stsukesh/sony-mhc-gn1300d-5.1-revival/tools/build_perfect_kicad_system.py

#!/usr/bin/env python3
"""
build_perfect_kicad_system.py
Generates the complete, pristine KiCad 10 hardware files for the Sony MHC-GN1300D 5.1 Revival.
Guarantees 100% clean loading in KiCad GUI and passing kicad-cli sch/pcb tools.
"""

import os
import uuid
import subprocess

BASE = "/run/media/stsukesh/Work/Revive SonyAudio sytem/hardware/sony-5.1-revival"
os.makedirs(f"{BASE}/libs", exist_ok=True)

ROOT_UUID = "936307ec-ff2e-4b68-b34e-0a0684a0c8b0"
SHEET_UUIDS = {
    "power_supply": "00000000-0000-0000-0000-000000000001",
    "amplifier": "00000000-0000-0000-0000-000000000002",
    "crossover_input": "00000000-0000-0000-0000-000000000003",
    "controller": "00000000-0000-0000-0000-000000000004",
    "protection": "00000000-0000-0000-0000-000000000005"
}

def make_uid():
    return str(uuid.uuid4())

# -------------------------------------------------------------
# 1. WRITE COMPLETE CUSTOM SYMBOL LIBRARY (sony-revival.kicad_sym)
# -------------------------------------------------------------
def build_custom_symbol_library():
    sym_path = f"{BASE}/libs/sony-revival.kicad_sym"
    content = """(kicad_symbol_lib
	(version 20231120)
	(generator "eeschema")
	(generator_version "10.0")
	(symbol "TPA3116D2"
		(in_bom yes)
		(on_board yes)
		(property "Reference" "U" (at -15.24 35.56 0) (effects (font (size 1.27 1.27))))
		(property "Value" "TPA3116D2" (at 5.08 35.56 0) (effects (font (size 1.27 1.27))))
		(property "Footprint" "Package_SO:HTSSOP-32-1EP_6.1x11mm_P0.65mm_EP5.2x11mm" (at 0 -40.64 0) (effects (font (size 1.27 1.27)) hide))
		(property "Datasheet" "http://www.ti.com/lit/ds/symlink/tpa3116d2.pdf" (at 0 -43.18 0) (effects (font (size 1.27 1.27)) hide))
		(property "Description" "50W Stereo / 100W Mono Class-D Audio Amplifier, HTSSOP-32" (at 0 -45.72 0) (effects (font (size 1.27 1.27)) hide))
		(symbol "TPA3116D2_0_1"
			(rectangle (start -15.24 33.02) (end 15.24 -38.1) (stroke (width 0.254) (type default)) (fill (type background)))
		)
		(symbol "TPA3116D2_1_1"
			(pin input line (at -17.78 30.48 0) (length 2.54) (name "MODSEL" (effects (font (size 1.27 1.27)))) (number "1" (effects (font (size 1.27 1.27)))))
			(pin input line (at -17.78 27.94 0) (length 2.54) (name "~{SD}" (effects (font (size 1.27 1.27)))) (number "2" (effects (font (size 1.27 1.27)))))
			(pin open_collector line (at -17.78 25.4 0) (length 2.54) (name "~{FAULT}" (effects (font (size 1.27 1.27)))) (number "3" (effects (font (size 1.27 1.27)))))
			(pin input line (at -17.78 20.32 0) (length 2.54) (name "INPL" (effects (font (size 1.27 1.27)))) (number "4" (effects (font (size 1.27 1.27)))))
			(pin input line (at -17.78 17.78 0) (length 2.54) (name "INNL" (effects (font (size 1.27 1.27)))) (number "5" (effects (font (size 1.27 1.27)))))
			(pin input line (at -17.78 12.7 0) (length 2.54) (name "PLIMIT" (effects (font (size 1.27 1.27)))) (number "6" (effects (font (size 1.27 1.27)))))
			(pin power_out line (at -17.78 7.62 0) (length 2.54) (name "GVDD" (effects (font (size 1.27 1.27)))) (number "7" (effects (font (size 1.27 1.27)))))
			(pin input line (at -17.78 2.54 0) (length 2.54) (name "GAIN/SLV" (effects (font (size 1.27 1.27)))) (number "8" (effects (font (size 1.27 1.27)))))
			(pin power_in line (at 0 -40.64 90) (length 2.54) (name "AGND" (effects (font (size 1.27 1.27)))) (number "9" (effects (font (size 1.27 1.27)))))
			(pin input line (at -17.78 -2.54 0) (length 2.54) (name "INNR" (effects (font (size 1.27 1.27)))) (number "10" (effects (font (size 1.27 1.27)))))
			(pin input line (at -17.78 -5.08 0) (length 2.54) (name "INPR" (effects (font (size 1.27 1.27)))) (number "11" (effects (font (size 1.27 1.27)))))
			(pin power_in line (at 17.78 30.48 180) (length 2.54) (name "PVCC" (effects (font (size 1.27 1.27)))) (number "16" (effects (font (size 1.27 1.27)))))
			(pin power_in line (at 17.78 27.94 180) (length 2.54) (name "PVCC" (effects (font (size 1.27 1.27)))) (number "17" (effects (font (size 1.27 1.27)))))
			(pin passive line (at 17.78 22.86 180) (length 2.54) (name "BSPR" (effects (font (size 1.27 1.27)))) (number "18" (effects (font (size 1.27 1.27)))))
			(pin output line (at 17.78 20.32 180) (length 2.54) (name "OUTPR" (effects (font (size 1.27 1.27)))) (number "19" (effects (font (size 1.27 1.27)))))
			(pin power_in line (at 2.54 -40.64 90) (length 2.54) (name "PGND" (effects (font (size 1.27 1.27)))) (number "20" (effects (font (size 1.27 1.27)))))
			(pin output line (at 17.78 15.24 180) (length 2.54) (name "OUTNR" (effects (font (size 1.27 1.27)))) (number "21" (effects (font (size 1.27 1.27)))))
			(pin passive line (at 17.78 12.7 180) (length 2.54) (name "BSNR" (effects (font (size 1.27 1.27)))) (number "22" (effects (font (size 1.27 1.27)))))
			(pin passive line (at 17.78 0 180) (length 2.54) (name "BSNL" (effects (font (size 1.27 1.27)))) (number "25" (effects (font (size 1.27 1.27)))))
			(pin output line (at 17.78 -2.54 180) (length 2.54) (name "OUTNL" (effects (font (size 1.27 1.27)))) (number "26" (effects (font (size 1.27 1.27)))))
			(pin power_in line (at 5.08 -40.64 90) (length 2.54) (name "PGND" (effects (font (size 1.27 1.27)))) (number "27" (effects (font (size 1.27 1.27)))))
			(pin output line (at 17.78 -7.62 180) (length 2.54) (name "OUTPL" (effects (font (size 1.27 1.27)))) (number "28" (effects (font (size 1.27 1.27)))))
			(pin passive line (at 17.78 -10.16 180) (length 2.54) (name "BSPL" (effects (font (size 1.27 1.27)))) (number "29" (effects (font (size 1.27 1.27)))))
			(pin power_in line (at 17.78 -15.24 180) (length 2.54) (name "PVCC" (effects (font (size 1.27 1.27)))) (number "30" (effects (font (size 1.27 1.27)))))
			(pin power_in line (at 17.78 -17.78 180) (length 2.54) (name "PVCC" (effects (font (size 1.27 1.27)))) (number "31" (effects (font (size 1.27 1.27)))))
			(pin power_in line (at -2.54 -40.64 90) (length 2.54) (name "AVCC" (effects (font (size 1.27 1.27)))) (number "32" (effects (font (size 1.27 1.27)))))
		)
	)
	(symbol "MCP4252"
		(in_bom yes)
		(on_board yes)
		(property "Reference" "U" (at -10.16 20.32 0) (effects (font (size 1.27 1.27))))
		(property "Value" "MCP4252" (at 5.08 20.32 0) (effects (font (size 1.27 1.27))))
		(property "Footprint" "Package_SO:SOIC-14_3.9x8.7mm_P1.27mm" (at 0 -22.86 0) (effects (font (size 1.27 1.27)) hide))
		(property "Datasheet" "https://ww1.microchip.com/downloads/en/DeviceDoc/22060b.pdf" (at 0 -25.4 0) (effects (font (size 1.27 1.27)) hide))
		(property "Description" "7/8-Bit Dual SPI Digital POT with Non-Volatile Memory" (at 0 -27.94 0) (effects (font (size 1.27 1.27)) hide))
		(symbol "MCP4252_0_1"
			(rectangle (start -10.16 17.78) (end 10.16 -20.32) (stroke (width 0.254) (type default)) (fill (type background)))
		)
		(symbol "MCP4252_1_1"
			(pin input line (at -12.7 15.24 0) (length 2.54) (name "~{CS}" (effects (font (size 1.27 1.27)))) (number "1" (effects (font (size 1.27 1.27)))))
			(pin input line (at -12.7 12.7 0) (length 2.54) (name "SCK" (effects (font (size 1.27 1.27)))) (number "2" (effects (font (size 1.27 1.27)))))
			(pin input line (at -12.7 10.16 0) (length 2.54) (name "SDI" (effects (font (size 1.27 1.27)))) (number "3" (effects (font (size 1.27 1.27)))))
			(pin power_in line (at 0 -22.86 90) (length 2.54) (name "VSS" (effects (font (size 1.27 1.27)))) (number "4" (effects (font (size 1.27 1.27)))))
			(pin passive line (at 12.7 5.08 180) (length 2.54) (name "P1B" (effects (font (size 1.27 1.27)))) (number "5" (effects (font (size 1.27 1.27)))))
			(pin passive line (at 12.7 7.62 180) (length 2.54) (name "P1W" (effects (font (size 1.27 1.27)))) (number "6" (effects (font (size 1.27 1.27)))))
			(pin passive line (at 12.7 10.16 180) (length 2.54) (name "P1A" (effects (font (size 1.27 1.27)))) (number "7" (effects (font (size 1.27 1.27)))))
			(pin passive line (at 12.7 -5.08 180) (length 2.54) (name "P0A" (effects (font (size 1.27 1.27)))) (number "8" (effects (font (size 1.27 1.27)))))
			(pin passive line (at 12.7 -7.62 180) (length 2.54) (name "P0W" (effects (font (size 1.27 1.27)))) (number "9" (effects (font (size 1.27 1.27)))))
			(pin passive line (at 12.7 -10.16 180) (length 2.54) (name "P0B" (effects (font (size 1.27 1.27)))) (number "10" (effects (font (size 1.27 1.27)))))
			(pin input line (at -12.7 0 0) (length 2.54) (name "~{WP}" (effects (font (size 1.27 1.27)))) (number "11" (effects (font (size 1.27 1.27)))))
			(pin input line (at -12.7 -2.54 0) (length 2.54) (name "~{SHDN}" (effects (font (size 1.27 1.27)))) (number "12" (effects (font (size 1.27 1.27)))))
			(pin output line (at -12.7 -7.62 0) (length 2.54) (name "SDO" (effects (font (size 1.27 1.27)))) (number "13" (effects (font (size 1.27 1.27)))))
			(pin power_in line (at 0 20.32 270) (length 2.54) (name "VDD" (effects (font (size 1.27 1.27)))) (number "14" (effects (font (size 1.27 1.27)))))
		)
	)
	(symbol "CD4052"
		(in_bom yes)
		(on_board yes)
		(property "Reference" "U" (at -10.16 22.86 0) (effects (font (size 1.27 1.27))))
		(property "Value" "CD4052" (at 5.08 22.86 0) (effects (font (size 1.27 1.27))))
		(property "Footprint" "Package_SO:SOIC-16_3.9x9.9mm_P1.27mm" (at 0 -25.4 0) (effects (font (size 1.27 1.27)) hide))
		(property "Datasheet" "http://www.ti.com/lit/ds/symlink/cd4052b.pdf" (at 0 -27.94 0) (effects (font (size 1.27 1.27)) hide))
		(property "Description" "Dual 4-Channel Analog Multiplexer / Demultiplexer" (at 0 -30.48 0) (effects (font (size 1.27 1.27)) hide))
		(symbol "CD4052_0_1"
			(rectangle (start -10.16 20.32) (end 10.16 -22.86) (stroke (width 0.254) (type default)) (fill (type background)))
		)
		(symbol "CD4052_1_1"
			(pin bidirectional line (at 12.7 15.24 180) (length 2.54) (name "Y0" (effects (font (size 1.27 1.27)))) (number "1" (effects (font (size 1.27 1.27)))))
			(pin bidirectional line (at 12.7 10.16 180) (length 2.54) (name "Y2" (effects (font (size 1.27 1.27)))) (number "2" (effects (font (size 1.27 1.27)))))
			(pin bidirectional line (at -12.7 12.7 0) (length 2.54) (name "Y_COM" (effects (font (size 1.27 1.27)))) (number "3" (effects (font (size 1.27 1.27)))))
			(pin bidirectional line (at 12.7 7.62 180) (length 2.54) (name "Y3" (effects (font (size 1.27 1.27)))) (number "4" (effects (font (size 1.27 1.27)))))
			(pin bidirectional line (at 12.7 12.7 180) (length 2.54) (name "Y1" (effects (font (size 1.27 1.27)))) (number "5" (effects (font (size 1.27 1.27)))))
			(pin input line (at -12.7 -15.24 0) (length 2.54) (name "INH" (effects (font (size 1.27 1.27)))) (number "6" (effects (font (size 1.27 1.27)))))
			(pin power_in line (at 2.54 -25.4 90) (length 2.54) (name "VEE" (effects (font (size 1.27 1.27)))) (number "7" (effects (font (size 1.27 1.27)))))
			(pin power_in line (at -2.54 -25.4 90) (length 2.54) (name "VSS" (effects (font (size 1.27 1.27)))) (number "8" (effects (font (size 1.27 1.27)))))
			(pin input line (at -12.7 -12.7 0) (length 2.54) (name "B" (effects (font (size 1.27 1.27)))) (number "9" (effects (font (size 1.27 1.27)))))
			(pin input line (at -12.7 -10.16 0) (length 2.54) (name "A" (effects (font (size 1.27 1.27)))) (number "10" (effects (font (size 1.27 1.27)))))
			(pin bidirectional line (at 12.7 -7.62 180) (length 2.54) (name "X3" (effects (font (size 1.27 1.27)))) (number "11" (effects (font (size 1.27 1.27)))))
			(pin bidirectional line (at 12.7 0 180) (length 2.54) (name "X0" (effects (font (size 1.27 1.27)))) (number "12" (effects (font (size 1.27 1.27)))))
			(pin bidirectional line (at -12.7 -2.54 0) (length 2.54) (name "X_COM" (effects (font (size 1.27 1.27)))) (number "13" (effects (font (size 1.27 1.27)))))
			(pin bidirectional line (at 12.7 -2.54 180) (length 2.54) (name "X1" (effects (font (size 1.27 1.27)))) (number "14" (effects (font (size 1.27 1.27)))))
			(pin bidirectional line (at 12.7 -5.08 180) (length 2.54) (name "X2" (effects (font (size 1.27 1.27)))) (number "15" (effects (font (size 1.27 1.27)))))
			(pin power_in line (at 0 22.86 270) (length 2.54) (name "VDD" (effects (font (size 1.27 1.27)))) (number "16" (effects (font (size 1.27 1.27)))))
		)
	)
	(symbol "QCC3008_MODULE"
		(in_bom yes)
		(on_board yes)
		(property "Reference" "U" (at -10.16 17.78 0) (effects (font (size 1.27 1.27))))
		(property "Value" "QCC3008_MODULE" (at 5.08 17.78 0) (effects (font (size 1.27 1.27))))
		(property "Footprint" "Connector_PinHeader_2.54mm:PinHeader_1x12_P2.54mm_Vertical" (at 0 -20.32 0) (effects (font (size 1.27 1.27)) hide))
		(property "Datasheet" "" (at 0 -22.86 0) (effects (font (size 1.27 1.27)) hide))
		(property "Description" "Qualcomm QCC3008 Bluetooth 5.0 Audio Module (aptX / aptX-LL)" (at 0 -25.4 0) (effects (font (size 1.27 1.27)) hide))
		(symbol "QCC3008_MODULE_0_1"
			(rectangle (start -10.16 15.24) (end 10.16 -17.78) (stroke (width 0.254) (type default)) (fill (type background)))
		)
		(symbol "QCC3008_MODULE_1_1"
			(pin power_in line (at 0 17.78 270) (length 2.54) (name "3V3" (effects (font (size 1.27 1.27)))) (number "1" (effects (font (size 1.27 1.27)))))
			(pin power_in line (at 0 -20.32 90) (length 2.54) (name "GND" (effects (font (size 1.27 1.27)))) (number "2" (effects (font (size 1.27 1.27)))))
			(pin output line (at 12.7 12.7 180) (length 2.54) (name "AOUTL_P" (effects (font (size 1.27 1.27)))) (number "3" (effects (font (size 1.27 1.27)))))
			(pin output line (at 12.7 10.16 180) (length 2.54) (name "AOUTL_N" (effects (font (size 1.27 1.27)))) (number "4" (effects (font (size 1.27 1.27)))))
			(pin output line (at 12.7 5.08 180) (length 2.54) (name "AOUTR_P" (effects (font (size 1.27 1.27)))) (number "5" (effects (font (size 1.27 1.27)))))
			(pin output line (at 12.7 2.54 180) (length 2.54) (name "AOUTR_N" (effects (font (size 1.27 1.27)))) (number "6" (effects (font (size 1.27 1.27)))))
			(pin output line (at 12.7 -2.54 180) (length 2.54) (name "SPDIF" (effects (font (size 1.27 1.27)))) (number "7" (effects (font (size 1.27 1.27)))))
			(pin input line (at -12.7 10.16 0) (length 2.54) (name "KEY" (effects (font (size 1.27 1.27)))) (number "8" (effects (font (size 1.27 1.27)))))
			(pin output line (at -12.7 5.08 0) (length 2.54) (name "LED1" (effects (font (size 1.27 1.27)))) (number "9" (effects (font (size 1.27 1.27)))))
			(pin output line (at -12.7 2.54 0) (length 2.54) (name "LED2" (effects (font (size 1.27 1.27)))) (number "10" (effects (font (size 1.27 1.27)))))
			(pin output line (at -12.7 -7.62 0) (length 2.54) (name "TX" (effects (font (size 1.27 1.27)))) (number "11" (effects (font (size 1.27 1.27)))))
			(pin input line (at -12.7 -10.16 0) (length 2.54) (name "RX" (effects (font (size 1.27 1.27)))) (number "12" (effects (font (size 1.27 1.27)))))
		)
	)
	(symbol "RELAY_SPST"
		(in_bom yes)
		(on_board yes)
		(property "Reference" "K" (at -7.62 10.16 0) (effects (font (size 1.27 1.27))))
		(property "Value" "RELAY_SPST" (at 2.54 10.16 0) (effects (font (size 1.27 1.27))))
		(property "Footprint" "Relay_THT:Relay_SPST_SANYOU_SRD_Series_Form_A" (at 0 -12.7 0) (effects (font (size 1.27 1.27)) hide))
		(property "Datasheet" "" (at 0 -15.24 0) (effects (font (size 1.27 1.27)) hide))
		(property "Description" "SPST Power Relay 10A 250VAC, 5V Coil" (at 0 -17.78 0) (effects (font (size 1.27 1.27)) hide))
		(symbol "RELAY_SPST_0_1"
			(rectangle (start -7.62 7.62) (end 7.62 -10.16) (stroke (width 0.254) (type default)) (fill (type background)))
		)
		(symbol "RELAY_SPST_1_1"
			(pin passive line (at -10.16 5.08 0) (length 2.54) (name "COIL+" (effects (font (size 1.27 1.27)))) (number "1" (effects (font (size 1.27 1.27)))))
			(pin passive line (at -10.16 -5.08 0) (length 2.54) (name "COIL-" (effects (font (size 1.27 1.27)))) (number "2" (effects (font (size 1.27 1.27)))))
			(pin passive line (at 10.16 5.08 180) (length 2.54) (name "COM" (effects (font (size 1.27 1.27)))) (number "3" (effects (font (size 1.27 1.27)))))
			(pin passive line (at 10.16 -5.08 180) (length 2.54) (name "NO" (effects (font (size 1.27 1.27)))) (number "4" (effects (font (size 1.27 1.27)))))
		)
	)
	(symbol "TLE2426"
		(in_bom yes)
		(on_board yes)
		(property "Reference" "U" (at -7.62 10.16 0) (effects (font (size 1.27 1.27))))
		(property "Value" "TLE2426" (at 2.54 10.16 0) (effects (font (size 1.27 1.27))))
		(property "Footprint" "Package_TO_SOT_THT:TO-92_Inline" (at 0 -12.7 0) (effects (font (size 1.27 1.27)) hide))
		(property "Datasheet" "http://www.ti.com/lit/ds/symlink/tle2426.pdf" (at 0 -15.24 0) (effects (font (size 1.27 1.27)) hide))
		(property "Description" "The 'Rail Splitter' Precision Virtual Ground" (at 0 -17.78 0) (effects (font (size 1.27 1.27)) hide))
		(symbol "TLE2426_0_1"
			(rectangle (start -7.62 7.62) (end 7.62 -10.16) (stroke (width 0.254) (type default)) (fill (type background)))
		)
		(symbol "TLE2426_1_1"
			(pin power_in line (at 0 10.16 270) (length 2.54) (name "IN" (effects (font (size 1.27 1.27)))) (number "1" (effects (font (size 1.27 1.27)))))
			(pin power_out line (at 10.16 0 180) (length 2.54) (name "OUT" (effects (font (size 1.27 1.27)))) (number "2" (effects (font (size 1.27 1.27)))))
			(pin power_in line (at 0 -12.7 90) (length 2.54) (name "COM" (effects (font (size 1.27 1.27)))) (number "3" (effects (font (size 1.27 1.27)))))
		)
	)
	(symbol "LM2596_5V"
		(in_bom yes)
		(on_board yes)
		(property "Reference" "U" (at -10.16 12.7 0) (effects (font (size 1.27 1.27))))
		(property "Value" "LM2596_5V" (at 2.54 12.7 0) (effects (font (size 1.27 1.27))))
		(property "Footprint" "Package_TO_SOT_SMD:TO-263-5_TabPin3" (at 0 -15.24 0) (effects (font (size 1.27 1.27)) hide))
		(property "Datasheet" "http://www.ti.com/lit/ds/symlink/lm2596.pdf" (at 0 -17.78 0) (effects (font (size 1.27 1.27)) hide))
		(property "Description" "SIMPLE SWITCHER 3A Step-Down Voltage Regulator, 5.0V Output" (at 0 -20.32 0) (effects (font (size 1.27 1.27)) hide))
		(symbol "LM2596_5V_0_1"
			(rectangle (start -10.16 10.16) (end 10.16 -12.7) (stroke (width 0.254) (type default)) (fill (type background)))
		)
		(symbol "LM2596_5V_1_1"
			(pin power_in line (at -12.7 7.62 0) (length 2.54) (name "VIN" (effects (font (size 1.27 1.27)))) (number "1" (effects (font (size 1.27 1.27)))))
			(pin power_out line (at 12.7 7.62 180) (length 2.54) (name "OUT" (effects (font (size 1.27 1.27)))) (number "2" (effects (font (size 1.27 1.27)))))
			(pin power_in line (at 0 -15.24 90) (length 2.54) (name "GND" (effects (font (size 1.27 1.27)))) (number "3" (effects (font (size 1.27 1.27)))))
			(pin input line (at 12.7 -5.08 180) (length 2.54) (name "FB" (effects (font (size 1.27 1.27)))) (number "4" (effects (font (size 1.27 1.27)))))
			(pin input line (at -12.7 -5.08 0) (length 2.54) (name "~{ON}/OFF" (effects (font (size 1.27 1.27)))) (number "5" (effects (font (size 1.27 1.27)))))
		)
	)
	(symbol "ESP32_WROOM_32"
		(in_bom yes)
		(on_board yes)
		(property "Reference" "U" (at -15.24 30.48 0) (effects (font (size 1.27 1.27))))
		(property "Value" "ESP32_WROOM_32" (at 5.08 30.48 0) (effects (font (size 1.27 1.27))))
		(property "Footprint" "RF_Module:ESP32-WROOM-32" (at 0 -33.02 0) (effects (font (size 1.27 1.27)) hide))
		(property "Datasheet" "https://www.espressif.com/sites/default/files/documentation/esp32-wroom-32_datasheet_en.pdf" (at 0 -35.56 0) (effects (font (size 1.27 1.27)) hide))
		(property "Description" "RF Module, ESP32-D0WDQ6 SoC, Wi-Fi 802.11b/g/n, Bluetooth, BLE, 32-bit, 2.7-3.6V" (at 0 -38.1 0) (effects (font (size 1.27 1.27)) hide))
		(symbol "ESP32_WROOM_32_0_1"
			(rectangle (start -15.24 27.94) (end 15.24 -30.48) (stroke (width 0.254) (type default)) (fill (type background)))
		)
		(symbol "ESP32_WROOM_32_1_1"
			(pin power_in line (at -17.78 25.4 0) (length 2.54) (name "3V3" (effects (font (size 1.27 1.27)))) (number "1" (effects (font (size 1.27 1.27)))))
			(pin input line (at -17.78 22.86 0) (length 2.54) (name "EN" (effects (font (size 1.27 1.27)))) (number "2" (effects (font (size 1.27 1.27)))))
			(pin input line (at -17.78 20.32 0) (length 2.54) (name "SENSOR_VP" (effects (font (size 1.27 1.27)))) (number "3" (effects (font (size 1.27 1.27)))))
			(pin input line (at -17.78 17.78 0) (length 2.54) (name "SENSOR_VN" (effects (font (size 1.27 1.27)))) (number "4" (effects (font (size 1.27 1.27)))))
			(pin input line (at -17.78 15.24 0) (length 2.54) (name "IO34" (effects (font (size 1.27 1.27)))) (number "5" (effects (font (size 1.27 1.27)))))
			(pin input line (at -17.78 12.7 0) (length 2.54) (name "IO35" (effects (font (size 1.27 1.27)))) (number "6" (effects (font (size 1.27 1.27)))))
			(pin bidirectional line (at -17.78 10.16 0) (length 2.54) (name "IO32" (effects (font (size 1.27 1.27)))) (number "7" (effects (font (size 1.27 1.27)))))
			(pin bidirectional line (at -17.78 7.62 0) (length 2.54) (name "IO33" (effects (font (size 1.27 1.27)))) (number "8" (effects (font (size 1.27 1.27)))))
			(pin bidirectional line (at -17.78 5.08 0) (length 2.54) (name "IO25" (effects (font (size 1.27 1.27)))) (number "9" (effects (font (size 1.27 1.27)))))
			(pin bidirectional line (at -17.78 2.54 0) (length 2.54) (name "IO26" (effects (font (size 1.27 1.27)))) (number "10" (effects (font (size 1.27 1.27)))))
			(pin bidirectional line (at -17.78 0 0) (length 2.54) (name "IO27" (effects (font (size 1.27 1.27)))) (number "11" (effects (font (size 1.27 1.27)))))
			(pin bidirectional line (at -17.78 -2.54 0) (length 2.54) (name "IO14" (effects (font (size 1.27 1.27)))) (number "12" (effects (font (size 1.27 1.27)))))
			(pin bidirectional line (at -17.78 -5.08 0) (length 2.54) (name "IO12" (effects (font (size 1.27 1.27)))) (number "13" (effects (font (size 1.27 1.27)))))
			(pin power_in line (at -17.78 -10.16 0) (length 2.54) (name "GND" (effects (font (size 1.27 1.27)))) (number "14" (effects (font (size 1.27 1.27)))))
			(pin bidirectional line (at 17.78 -5.08 180) (length 2.54) (name "IO13" (effects (font (size 1.27 1.27)))) (number "15" (effects (font (size 1.27 1.27)))))
			(pin bidirectional line (at 17.78 -2.54 180) (length 2.54) (name "IO15" (effects (font (size 1.27 1.27)))) (number "16" (effects (font (size 1.27 1.27)))))
			(pin bidirectional line (at 17.78 0 180) (length 2.54) (name "IO2" (effects (font (size 1.27 1.27)))) (number "17" (effects (font (size 1.27 1.27)))))
			(pin bidirectional line (at 17.78 2.54 180) (length 2.54) (name "IO0" (effects (font (size 1.27 1.27)))) (number "18" (effects (font (size 1.27 1.27)))))
			(pin bidirectional line (at 17.78 5.08 180) (length 2.54) (name "IO4" (effects (font (size 1.27 1.27)))) (number "19" (effects (font (size 1.27 1.27)))))
			(pin bidirectional line (at 17.78 7.62 180) (length 2.54) (name "IO16" (effects (font (size 1.27 1.27)))) (number "20" (effects (font (size 1.27 1.27)))))
			(pin bidirectional line (at 17.78 10.16 180) (length 2.54) (name "IO17" (effects (font (size 1.27 1.27)))) (number "21" (effects (font (size 1.27 1.27)))))
			(pin bidirectional line (at 17.78 12.7 180) (length 2.54) (name "IO5" (effects (font (size 1.27 1.27)))) (number "22" (effects (font (size 1.27 1.27)))))
			(pin bidirectional line (at 17.78 15.24 180) (length 2.54) (name "IO18" (effects (font (size 1.27 1.27)))) (number "23" (effects (font (size 1.27 1.27)))))
			(pin bidirectional line (at 17.78 17.78 180) (length 2.54) (name "IO19" (effects (font (size 1.27 1.27)))) (number "24" (effects (font (size 1.27 1.27)))))
			(pin bidirectional line (at 17.78 20.32 180) (length 2.54) (name "IO21" (effects (font (size 1.27 1.27)))) (number "25" (effects (font (size 1.27 1.27)))))
			(pin bidirectional line (at 17.78 22.86 180) (length 2.54) (name "IO22" (effects (font (size 1.27 1.27)))) (number "26" (effects (font (size 1.27 1.27)))))
			(pin bidirectional line (at 17.78 25.4 180) (length 2.54) (name "IO23" (effects (font (size 1.27 1.27)))) (number "27" (effects (font (size 1.27 1.27)))))
			(pin output line (at 17.78 27.94 180) (length 2.54) (name "TXD0" (effects (font (size 1.27 1.27)))) (number "28" (effects (font (size 1.27 1.27)))))
			(pin input line (at 17.78 30.48 180) (length 2.54) (name "RXD0" (effects (font (size 1.27 1.27)))) (number "29" (effects (font (size 1.27 1.27)))))
			(pin power_in line (at 0 -33.02 90) (length 2.54) (name "GND" (effects (font (size 1.27 1.27)))) (number "38" (effects (font (size 1.27 1.27)))))
		)
	)
	(symbol "NE5532"
		(in_bom yes)
		(on_board yes)
		(property "Reference" "U" (at -7.62 12.7 0) (effects (font (size 1.27 1.27))))
		(property "Value" "NE5532" (at 2.54 12.7 0) (effects (font (size 1.27 1.27))))
		(property "Footprint" "Package_SO:SOIC-8_3.9x4.9mm_P1.27mm" (at 0 -15.24 0) (effects (font (size 1.27 1.27)) hide))
		(property "Datasheet" "http://www.ti.com/lit/ds/symlink/ne5532.pdf" (at 0 -17.78 0) (effects (font (size 1.27 1.27)) hide))
		(property "Description" "Dual Low-Noise Operational Amplifier, DIP-8/SOIC-8" (at 0 -20.32 0) (effects (font (size 1.27 1.27)) hide))
		(symbol "NE5532_0_1"
			(rectangle (start -10.16 10.16) (end 10.16 -12.7) (stroke (width 0.254) (type default)) (fill (type background)))
		)
		(symbol "NE5532_1_1"
			(pin output line (at 12.7 7.62 180) (length 2.54) (name "OUTA" (effects (font (size 1.27 1.27)))) (number "1" (effects (font (size 1.27 1.27)))))
			(pin input line (at -12.7 7.62 0) (length 2.54) (name "-INA" (effects (font (size 1.27 1.27)))) (number "2" (effects (font (size 1.27 1.27)))))
			(pin input line (at -12.7 2.54 0) (length 2.54) (name "+INA" (effects (font (size 1.27 1.27)))) (number "3" (effects (font (size 1.27 1.27)))))
			(pin power_in line (at 0 -15.24 90) (length 2.54) (name "V-" (effects (font (size 1.27 1.27)))) (number "4" (effects (font (size 1.27 1.27)))))
			(pin input line (at -12.7 -2.54 0) (length 2.54) (name "+INB" (effects (font (size 1.27 1.27)))) (number "5" (effects (font (size 1.27 1.27)))))
			(pin input line (at -12.7 -7.62 0) (length 2.54) (name "-INB" (effects (font (size 1.27 1.27)))) (number "6" (effects (font (size 1.27 1.27)))))
			(pin output line (at 12.7 -7.62 180) (length 2.54) (name "OUTB" (effects (font (size 1.27 1.27)))) (number "7" (effects (font (size 1.27 1.27)))))
			(pin power_in line (at 0 12.7 270) (length 2.54) (name "V+" (effects (font (size 1.27 1.27)))) (number "8" (effects (font (size 1.27 1.27)))))
		)
	)
	(symbol "KBU810"
		(in_bom yes)
		(on_board yes)
		(property "Reference" "BR" (at -7.62 10.16 0) (effects (font (size 1.27 1.27))))
		(property "Value" "KBU810" (at 2.54 10.16 0) (effects (font (size 1.27 1.27))))
		(property "Footprint" "Diode_THT:Diode_Bridge_Vishay_KBU" (at 0 -12.7 0) (effects (font (size 1.27 1.27)) hide))
		(property "Datasheet" "https://www.vishay.com/docs/88657/kbu8a.pdf" (at 0 -15.24 0) (effects (font (size 1.27 1.27)) hide))
		(property "Description" "Single-Phase Bridge Rectifier, 8.0A, 1000V" (at 0 -17.78 0) (effects (font (size 1.27 1.27)) hide))
		(symbol "KBU810_0_1"
			(rectangle (start -7.62 7.62) (end 7.62 -10.16) (stroke (width 0.254) (type default)) (fill (type background)))
		)
		(symbol "KBU810_1_1"
			(pin power_out line (at 10.16 5.08 180) (length 2.54) (name "+" (effects (font (size 1.27 1.27)))) (number "1" (effects (font (size 1.27 1.27)))))
			(pin passive line (at -10.16 5.08 0) (length 2.54) (name "~" (effects (font (size 1.27 1.27)))) (number "2" (effects (font (size 1.27 1.27)))))
			(pin passive line (at -10.16 -5.08 0) (length 2.54) (name "~" (effects (font (size 1.27 1.27)))) (number "3" (effects (font (size 1.27 1.27)))))
			(pin power_out line (at 10.16 -5.08 180) (length 2.54) (name "-" (effects (font (size 1.27 1.27)))) (number "4" (effects (font (size 1.27 1.27)))))
		)
	)
	(symbol "AMS1117_3V3"
		(in_bom yes)
		(on_board yes)
		(property "Reference" "U" (at -7.62 10.16 0) (effects (font (size 1.27 1.27))))
		(property "Value" "AMS1117_3V3" (at 2.54 10.16 0) (effects (font (size 1.27 1.27))))
		(property "Footprint" "Package_TO_SOT_SMD:SOT-223-3_TabPin2" (at 0 -12.7 0) (effects (font (size 1.27 1.27)) hide))
		(property "Datasheet" "http://www.advanced-monolithic.com/pdf/ds1117.pdf" (at 0 -15.24 0) (effects (font (size 1.27 1.27)) hide))
		(property "Description" "1A Low Dropout Linear Regulator, 3.3V Output" (at 0 -17.78 0) (effects (font (size 1.27 1.27)) hide))
		(symbol "AMS1117_3V3_0_1"
			(rectangle (start -7.62 7.62) (end 7.62 -10.16) (stroke (width 0.254) (type default)) (fill (type background)))
		)
		(symbol "AMS1117_3V3_1_1"
			(pin power_in line (at 0 -12.7 90) (length 2.54) (name "GND" (effects (font (size 1.27 1.27)))) (number "1" (effects (font (size 1.27 1.27)))))
			(pin power_out line (at 10.16 0 180) (length 2.54) (name "VOUT" (effects (font (size 1.27 1.27)))) (number "2" (effects (font (size 1.27 1.27)))))
			(pin power_in line (at -10.16 0 0) (length 2.54) (name "VIN" (effects (font (size 1.27 1.27)))) (number "3" (effects (font (size 1.27 1.27)))))
		)
	)
	(symbol "2N2222"
		(in_bom yes)
		(on_board yes)
		(property "Reference" "Q" (at -5.08 7.62 0) (effects (font (size 1.27 1.27))))
		(property "Value" "2N2222" (at 2.54 7.62 0) (effects (font (size 1.27 1.27))))
		(property "Footprint" "Package_TO_SOT_THT:TO-92_Inline" (at 0 -10.16 0) (effects (font (size 1.27 1.27)) hide))
		(property "Datasheet" "" (at 0 -12.7 0) (effects (font (size 1.27 1.27)) hide))
		(property "Description" "NPN BJT Transistor 40V 0.8A" (at 0 -15.24 0) (effects (font (size 1.27 1.27)) hide))
		(symbol "2N2222_0_1"
			(rectangle (start -5.08 5.08) (end 5.08 -7.62) (stroke (width 0.254) (type default)) (fill (type background)))
		)
		(symbol "2N2222_1_1"
			(pin input line (at -7.62 0 0) (length 2.54) (name "B" (effects (font (size 1.27 1.27)))) (number "1" (effects (font (size 1.27 1.27)))))
			(pin passive line (at 7.62 2.54 180) (length 2.54) (name "C" (effects (font (size 1.27 1.27)))) (number "2" (effects (font (size 1.27 1.27)))))
			(pin passive line (at 7.62 -2.54 180) (length 2.54) (name "E" (effects (font (size 1.27 1.27)))) (number "3" (effects (font (size 1.27 1.27)))))
		)
	)
	(symbol "TSOP1738"
		(in_bom yes)
		(on_board yes)
		(property "Reference" "U" (at -5.08 7.62 0) (effects (font (size 1.27 1.27))))
		(property "Value" "TSOP1738" (at 2.54 7.62 0) (effects (font (size 1.27 1.27))))
		(property "Footprint" "OptoDevice:Vishay_MINIMOLD-3Pin" (at 0 -10.16 0) (effects (font (size 1.27 1.27)) hide))
		(property "Datasheet" "https://www.vishay.com/docs/82006/tsop17xx.pdf" (at 0 -12.7 0) (effects (font (size 1.27 1.27)) hide))
		(property "Description" "Photo Modules for PCM Remote Control Systems, 38kHz" (at 0 -15.24 0) (effects (font (size 1.27 1.27)) hide))
		(symbol "TSOP1738_0_1"
			(rectangle (start -5.08 5.08) (end 5.08 -7.62) (stroke (width 0.254) (type default)) (fill (type background)))
		)
		(symbol "TSOP1738_1_1"
			(pin output line (at 7.62 0 180) (length 2.54) (name "OUT" (effects (font (size 1.27 1.27)))) (number "1" (effects (font (size 1.27 1.27)))))
			(pin power_in line (at 0 -10.16 90) (length 2.54) (name "GND" (effects (font (size 1.27 1.27)))) (number "2" (effects (font (size 1.27 1.27)))))
			(pin power_in line (at 0 7.62 270) (length 2.54) (name "VS" (effects (font (size 1.27 1.27)))) (number "3" (effects (font (size 1.27 1.27)))))
		)
	)
)
"""
    with open(sym_path, "w") as f:
        f.write(content)
    print("Custom symbol library generated.")

# -------------------------------------------------------------
# 2. EMBEDDED SYMBOLS BLOCK FOR ALL SCHEMATICS
# -------------------------------------------------------------
def get_common_lib_symbols():
    sym_file = f"{BASE}/libs/sony-revival.kicad_sym"
    with open(sym_file, "r") as f:
        sym_content = f.read()
    
    inner = sym_content.replace('(kicad_symbol_lib\n\t(version 20231120)\n\t(generator "eeschema")\n\t(generator_version "10.0")', '')
    if inner.endswith(')\n'):
        inner = inner[:-2]
    elif inner.endswith(')'):
        inner = inner[:-1]
        
    device_symbols = """
		(symbol "Device:R"
			(pin_numbers (hide yes))
			(pin_names (offset 0))
			(exclude_from_sim no)
			(in_bom yes)
			(on_board yes)
			(property "Reference" "R" (at 2.032 0 90) (effects (font (size 1.27 1.27))))
			(property "Value" "R" (at 0 0 90) (effects (font (size 1.27 1.27))))
			(property "Footprint" "" (at -1.778 0 90) (effects (font (size 0.762 0.762))))
			(property "Datasheet" "" (at 0 0 0) (effects (font (size 0.762 0.762))))
			(property "Description" "Resistor" (at 0 0 0) (effects (font (size 1.27 1.27))))
			(symbol "R_0_1"
				(rectangle (start -1.016 2.54) (end 1.016 -2.54) (stroke (width 0.254) (type default)) (fill (type none)))
			)
			(symbol "R_1_1"
				(pin passive line (at 0 3.81 270) (length 1.27) (name "~" (effects (font (size 1.27 1.27)))) (number "1" (effects (font (size 1.27 1.27)))))
				(pin passive line (at 0 -3.81 90) (length 1.27) (name "~" (effects (font (size 1.27 1.27)))) (number "2" (effects (font (size 1.27 1.27)))))
			)
		)
		(symbol "Device:C"
			(pin_numbers (hide yes))
			(pin_names (offset 0))
			(exclude_from_sim no)
			(in_bom yes)
			(on_board yes)
			(property "Reference" "C" (at 0.635 2.54 0) (effects (font (size 1.27 1.27))))
			(property "Value" "C" (at 0.635 -2.54 0) (effects (font (size 1.27 1.27))))
			(property "Footprint" "" (at 0 0 0) (effects (font (size 0.762 0.762))))
			(property "Datasheet" "" (at 0 0 0) (effects (font (size 0.762 0.762))))
			(property "Description" "Unpolarized capacitor" (at 0 0 0) (effects (font (size 1.27 1.27))))
			(symbol "C_0_1"
				(polyline (pts (xy -2.032 -0.762) (xy 2.032 -0.762)) (stroke (width 0.508) (type default)) (fill (type none)))
				(polyline (pts (xy -2.032 0.762) (xy 2.032 0.762)) (stroke (width 0.508) (type default)) (fill (type none)))
			)
			(symbol "C_1_1"
				(pin passive line (at 0 3.81 270) (length 3.048) (name "~" (effects (font (size 1.27 1.27)))) (number "1" (effects (font (size 1.27 1.27)))))
				(pin passive line (at 0 -3.81 90) (length 3.048) (name "~" (effects (font (size 1.27 1.27)))) (number "2" (effects (font (size 1.27 1.27)))))
			)
		)
		(symbol "Device:C_Polarized"
			(pin_numbers (hide yes))
			(pin_names (offset 0))
			(exclude_from_sim no)
			(in_bom yes)
			(on_board yes)
			(property "Reference" "C" (at 1.27 2.54 0) (effects (font (size 1.27 1.27))))
			(property "Value" "C_Polarized" (at 1.27 -2.54 0) (effects (font (size 1.27 1.27))))
			(property "Footprint" "" (at 0 0 0) (effects (font (size 0.762 0.762))))
			(property "Datasheet" "" (at 0 0 0) (effects (font (size 0.762 0.762))))
			(property "Description" "Polarized capacitor" (at 0 0 0) (effects (font (size 1.27 1.27))))
			(symbol "C_Polarized_0_1"
				(polyline (pts (xy -2.032 -0.762) (xy 2.032 -0.762)) (stroke (width 0.508) (type default)) (fill (type none)))
				(polyline (pts (xy -2.032 0.762) (xy 2.032 0.762)) (stroke (width 0.508) (type default)) (fill (type none)))
			)
			(symbol "C_Polarized_1_1"
				(pin passive line (at 0 3.81 270) (length 3.048) (name "+" (effects (font (size 1.27 1.27)))) (number "1" (effects (font (size 1.27 1.27)))))
				(pin passive line (at 0 -3.81 90) (length 3.048) (name "-" (effects (font (size 1.27 1.27)))) (number "2" (effects (font (size 1.27 1.27)))))
			)
		)
		(symbol "Device:L"
			(pin_numbers (hide yes))
			(pin_names (offset 0))
			(exclude_from_sim no)
			(in_bom yes)
			(on_board yes)
			(property "Reference" "L" (at 1.27 0 90) (effects (font (size 1.27 1.27))))
			(property "Value" "L" (at -1.27 0 90) (effects (font (size 1.27 1.27))))
			(property "Footprint" "" (at 0 0 0) (effects (font (size 0.762 0.762))))
			(property "Datasheet" "" (at 0 0 0) (effects (font (size 0.762 0.762))))
			(property "Description" "Inductor" (at 0 0 0) (effects (font (size 1.27 1.27))))
			(symbol "L_0_1"
				(arc (start 0 -2.54) (mid 1.27 -1.27) (end 0 0) (stroke (width 0.254) (type default)) (fill (type none)))
				(arc (start 0 0) (mid 1.27 1.27) (end 0 2.54) (stroke (width 0.254) (type default)) (fill (type none)))
			)
			(symbol "L_1_1"
				(pin passive line (at 0 3.81 270) (length 1.27) (name "~" (effects (font (size 1.27 1.27)))) (number "1" (effects (font (size 1.27 1.27)))))
				(pin passive line (at 0 -3.81 90) (length 1.27) (name "~" (effects (font (size 1.27 1.27)))) (number "2" (effects (font (size 1.27 1.27)))))
			)
		)
		(symbol "Device:D"
			(pin_numbers (hide yes))
			(pin_names (offset 0))
			(exclude_from_sim no)
			(in_bom yes)
			(on_board yes)
			(property "Reference" "D" (at 0 2.54 0) (effects (font (size 1.27 1.27))))
			(property "Value" "D" (at 0 -2.54 0) (effects (font (size 1.27 1.27))))
			(property "Footprint" "" (at 0 0 0) (effects (font (size 0.762 0.762))))
			(property "Datasheet" "" (at 0 0 0) (effects (font (size 0.762 0.762))))
			(property "Description" "Diode" (at 0 0 0) (effects (font (size 1.27 1.27))))
			(symbol "D_0_1"
				(polyline (pts (xy -1.27 -1.27) (xy 1.27 0) (xy -1.27 1.27) (xy -1.27 -1.27)) (stroke (width 0.254) (type default)) (fill (type outline)))
				(polyline (pts (xy 1.27 -1.27) (xy 1.27 1.27)) (stroke (width 0.254) (type default)) (fill (type none)))
			)
			(symbol "D_1_1"
				(pin passive line (at -3.81 0 0) (length 2.54) (name "A" (effects (font (size 1.27 1.27)))) (number "1" (effects (font (size 1.27 1.27)))))
				(pin passive line (at 3.81 0 180) (length 2.54) (name "K" (effects (font (size 1.27 1.27)))) (number "2" (effects (font (size 1.27 1.27)))))
			)
		)
		(symbol "Connector:Conn_01x02"
			(pin_names (offset 1.016))
			(exclude_from_sim no)
			(in_bom yes)
			(on_board yes)
			(property "Reference" "J" (at 0 2.54 0) (effects (font (size 1.27 1.27))))
			(property "Value" "Conn_01x02" (at 0 -5.08 0) (effects (font (size 1.27 1.27))))
			(property "Footprint" "" (at 0 0 0) (effects (font (size 0.762 0.762))))
			(property "Datasheet" "" (at 0 0 0) (effects (font (size 0.762 0.762))))
			(property "Description" "Generic connector, single row, 01x02" (at 0 0 0) (effects (font (size 1.27 1.27))))
			(symbol "Conn_01x02_0_1"
				(rectangle (start -1.27 1.27) (end 1.27 -3.81) (stroke (width 0.254) (type default)) (fill (type background)))
			)
			(symbol "Conn_01x02_1_1"
				(pin passive line (at -3.81 0 0) (length 2.54) (name "1" (effects (font (size 1.27 1.27)))) (number "1" (effects (font (size 1.27 1.27)))))
				(pin passive line (at -3.81 -2.54 0) (length 2.54) (name "2" (effects (font (size 1.27 1.27)))) (number "2" (effects (font (size 1.27 1.27)))))
			)
		)
		(symbol "Connector:Conn_01x03"
			(pin_names (offset 1.016))
			(exclude_from_sim no)
			(in_bom yes)
			(on_board yes)
			(property "Reference" "J" (at 0 3.81 0) (effects (font (size 1.27 1.27))))
			(property "Value" "Conn_01x03" (at 0 -6.35 0) (effects (font (size 1.27 1.27))))
			(property "Footprint" "" (at 0 0 0) (effects (font (size 0.762 0.762))))
			(property "Datasheet" "" (at 0 0 0) (effects (font (size 0.762 0.762))))
			(property "Description" "Generic connector, single row, 01x03" (at 0 0 0) (effects (font (size 1.27 1.27))))
			(symbol "Conn_01x03_0_1"
				(rectangle (start -1.27 2.54) (end 1.27 -5.08) (stroke (width 0.254) (type default)) (fill (type background)))
			)
			(symbol "Conn_01x03_1_1"
				(pin passive line (at -3.81 1.27 0) (length 2.54) (name "1" (effects (font (size 1.27 1.27)))) (number "1" (effects (font (size 1.27 1.27)))))
				(pin passive line (at -3.81 -1.27 0) (length 2.54) (name "2" (effects (font (size 1.27 1.27)))) (number "2" (effects (font (size 1.27 1.27)))))
				(pin passive line (at -3.81 -3.81 0) (length 2.54) (name "3" (effects (font (size 1.27 1.27)))) (number "3" (effects (font (size 1.27 1.27)))))
			)
		)
		(symbol "Connector:Conn_01x04"
			(pin_names (offset 1.016))
			(exclude_from_sim no)
			(in_bom yes)
			(on_board yes)
			(property "Reference" "J" (at 0 5.08 0) (effects (font (size 1.27 1.27))))
			(property "Value" "Conn_01x04" (at 0 -7.62 0) (effects (font (size 1.27 1.27))))
			(property "Footprint" "" (at 0 0 0) (effects (font (size 0.762 0.762))))
			(property "Datasheet" "" (at 0 0 0) (effects (font (size 0.762 0.762))))
			(property "Description" "Generic connector, single row, 01x04" (at 0 0 0) (effects (font (size 1.27 1.27))))
			(symbol "Conn_01x04_0_1"
				(rectangle (start -1.27 3.81) (end 1.27 -6.35) (stroke (width 0.254) (type default)) (fill (type background)))
			)
			(symbol "Conn_01x04_1_1"
				(pin passive line (at -3.81 2.54 0) (length 2.54) (name "1" (effects (font (size 1.27 1.27)))) (number "1" (effects (font (size 1.27 1.27)))))
				(pin passive line (at -3.81 0 0) (length 2.54) (name "2" (effects (font (size 1.27 1.27)))) (number "2" (effects (font (size 1.27 1.27)))))
				(pin passive line (at -3.81 -2.54 0) (length 2.54) (name "3" (effects (font (size 1.27 1.27)))) (number "3" (effects (font (size 1.27 1.27)))))
				(pin passive line (at -3.81 -5.08 0) (length 2.54) (name "4" (effects (font (size 1.27 1.27)))) (number "4" (effects (font (size 1.27 1.27)))))
			)
		)
		(symbol "Connector:Conn_01x05"
			(pin_names (offset 1.016))
			(exclude_from_sim no)
			(in_bom yes)
			(on_board yes)
			(property "Reference" "J" (at 0 6.35 0) (effects (font (size 1.27 1.27))))
			(property "Value" "Conn_01x05" (at 0 -8.89 0) (effects (font (size 1.27 1.27))))
			(property "Footprint" "" (at 0 0 0) (effects (font (size 0.762 0.762))))
			(property "Datasheet" "" (at 0 0 0) (effects (font (size 0.762 0.762))))
			(property "Description" "Generic connector, single row, 01x05" (at 0 0 0) (effects (font (size 1.27 1.27))))
			(symbol "Conn_01x05_0_1"
				(rectangle (start -1.27 5.08) (end 1.27 -7.62) (stroke (width 0.254) (type default)) (fill (type background)))
			)
			(symbol "Conn_01x05_1_1"
				(pin passive line (at -3.81 3.81 0) (length 2.54) (name "1" (effects (font (size 1.27 1.27)))) (number "1" (effects (font (size 1.27 1.27)))))
				(pin passive line (at -3.81 1.27 0) (length 2.54) (name "2" (effects (font (size 1.27 1.27)))) (number "2" (effects (font (size 1.27 1.27)))))
				(pin passive line (at -3.81 -1.27 0) (length 2.54) (name "3" (effects (font (size 1.27 1.27)))) (number "3" (effects (font (size 1.27 1.27)))))
				(pin passive line (at -3.81 -3.81 0) (length 2.54) (name "4" (effects (font (size 1.27 1.27)))) (number "4" (effects (font (size 1.27 1.27)))))
				(pin passive line (at -3.81 -6.35 0) (length 2.54) (name "5" (effects (font (size 1.27 1.27)))) (number "5" (effects (font (size 1.27 1.27)))))
			)
		)
		(symbol "Connector:Conn_01x07"
			(pin_names (offset 1.016))
			(exclude_from_sim no)
			(in_bom yes)
			(on_board yes)
			(property "Reference" "J" (at 0 8.89 0) (effects (font (size 1.27 1.27))))
			(property "Value" "Conn_01x07" (at 0 -11.43 0) (effects (font (size 1.27 1.27))))
			(property "Footprint" "" (at 0 0 0) (effects (font (size 0.762 0.762))))
			(property "Datasheet" "" (at 0 0 0) (effects (font (size 0.762 0.762))))
			(property "Description" "Generic connector, single row, 01x07" (at 0 0 0) (effects (font (size 1.27 1.27))))
			(symbol "Conn_01x07_0_1"
				(rectangle (start -1.27 7.62) (end 1.27 -10.16) (stroke (width 0.254) (type default)) (fill (type background)))
			)
			(symbol "Conn_01x07_1_1"
				(pin passive line (at -3.81 6.35 0) (length 2.54) (name "1" (effects (font (size 1.27 1.27)))) (number "1" (effects (font (size 1.27 1.27)))))
				(pin passive line (at -3.81 3.81 0) (length 2.54) (name "2" (effects (font (size 1.27 1.27)))) (number "2" (effects (font (size 1.27 1.27)))))
				(pin passive line (at -3.81 1.27 0) (length 2.54) (name "3" (effects (font (size 1.27 1.27)))) (number "3" (effects (font (size 1.27 1.27)))))
				(pin passive line (at -3.81 -1.27 0) (length 2.54) (name "4" (effects (font (size 1.27 1.27)))) (number "4" (effects (font (size 1.27 1.27)))))
				(pin passive line (at -3.81 -3.81 0) (length 2.54) (name "5" (effects (font (size 1.27 1.27)))) (number "5" (effects (font (size 1.27 1.27)))))
				(pin passive line (at -3.81 -6.35 0) (length 2.54) (name "6" (effects (font (size 1.27 1.27)))) (number "6" (effects (font (size 1.27 1.27)))))
				(pin passive line (at -3.81 -8.89 0) (length 2.54) (name "7" (effects (font (size 1.27 1.27)))) (number "7" (effects (font (size 1.27 1.27)))))
			)
		)
"""
    return inner + "\n" + device_symbols

def generate_placed_symbol(lib_id, ref, val, x, y, angle, sheet_path, pin_count=2, footprint="", datasheet=""):
    s_lines = []
    s_lines.append('\t(symbol')
    s_lines.append(f'\t\t(lib_id "{lib_id}")')
    s_lines.append(f'\t\t(at {x:.2f} {y:.2f} {angle})')
    s_lines.append('\t\t(unit 1)')
    s_lines.append('\t\t(exclude_from_sim no)')
    s_lines.append('\t\t(in_bom yes)')
    s_lines.append('\t\t(on_board yes)')
    s_lines.append('\t\t(dnp no)')
    s_lines.append(f'\t\t(uuid "{make_uid()}")')
    s_lines.append(f'\t\t(property "Reference" "{ref}" (at {x+2.54:.2f} {y:.2f} 0) (effects (font (size 1.27 1.27))))')
    s_lines.append(f'\t\t(property "Value" "{val}" (at {x+2.54:.2f} {y-2.54:.2f} 0) (effects (font (size 1.27 1.27))))')
    s_lines.append(f'\t\t(property "Footprint" "{footprint}" (at {x:.2f} {y:.2f} 0) (effects (font (size 1.27 1.27)) (hide yes)))')
    s_lines.append(f'\t\t(property "Datasheet" "{datasheet}" (at {x:.2f} {y:.2f} 0) (effects (font (size 1.27 1.27)) (hide yes)))')
    s_lines.append(f'\t\t(property "Description" "" (at {x:.2f} {y:.2f} 0) (effects (font (size 1.27 1.27)) (hide yes)))')
    
    for p in range(1, pin_count + 1):
        s_lines.append(f'\t\t(pin "{p}" (uuid "{make_uid()}"))')
        
    s_lines.append('\t\t(instances')
    s_lines.append('\t\t\t(project "sony-5.1-revival"')
    s_lines.append(f'\t\t\t\t(path "{sheet_path}"')
    s_lines.append(f'\t\t\t\t\t(reference "{ref}")')
    s_lines.append('\t\t\t\t\t(unit 1)')
    s_lines.append('\t\t\t\t)')
    s_lines.append('\t\t\t)')
    s_lines.append('\t\t)')
    s_lines.append('\t)')
    return '\n'.join(s_lines)

# -------------------------------------------------------------
# 3. BUILD ROOT HIERARCHICAL SCHEMATIC
# -------------------------------------------------------------
def build_root_schematic():
    lines = []
    lines.append('(kicad_sch')
    lines.append('\t(version 20250114)')
    lines.append('\t(generator "eeschema")')
    lines.append('\t(generator_version "10.0")')
    lines.append(f'\t(uuid "{ROOT_UUID}")')
    lines.append('\t(paper "A3")')
    lines.append('\t(title_block')
    lines.append('\t\t(title "Sony MHC-GN1300D 5.1 System Revival - Master Schematic")')
    lines.append('\t\t(date "2026-09-06")')
    lines.append('\t\t(rev "1.0")')
    lines.append('\t\t(comment 1 "Unified 5.1 Class-D Amp + Active Crossover + ESP32 Web/Serial Hub")')
    lines.append('\t\t(comment 2 "Target Fabrication: Lion Circuits India (150x200mm 2-Layer FR4)")')
    lines.append('\t)')
    lines.append('\t(lib_symbols)')
    
    sheets_info = [
        ("Power Supply Subsystem", "power_supply.kicad_sch", SHEET_UUIDS["power_supply"], 50.8, 50.8, "2"),
        ("Amplifier Subsystem", "amplifier.kicad_sch", SHEET_UUIDS["amplifier"], 152.4, 50.8, "3"),
        ("Crossover & Input Subsystem", "crossover_input.kicad_sch", SHEET_UUIDS["crossover_input"], 254.0, 50.8, "4"),
        ("ESP32 Controller Subsystem", "controller.kicad_sch", SHEET_UUIDS["controller"], 50.8, 127.0, "5"),
        ("Protection & Terminals", "protection.kicad_sch", SHEET_UUIDS["protection"], 152.4, 127.0, "6")
    ]
    
    for name, filename, suuid, x, y, pg in sheets_info:
        lines.append('\t(sheet')
        lines.append(f'\t\t(at {x:.2f} {y:.2f})')
        lines.append('\t\t(size 76.2 45.72)')
        lines.append('\t\t(fields_autoplaced yes)')
        lines.append('\t\t(stroke (width 0) (type solid))')
        lines.append('\t\t(fill (color 0 0 0 0.0000))')
        lines.append(f'\t\t(uuid "{suuid}")')
        lines.append(f'\t\t(property "Sheetname" "{name}" (at {x:.2f} {y-2.54:.2f} 0) (effects (font (size 1.524 1.524)) (justify left bottom)))')
        lines.append(f'\t\t(property "Sheetfile" "{filename}" (at {x:.2f} {y+48.26:.2f} 0) (effects (font (size 1.27 1.27)) (justify left top)))')
        lines.append('\t\t(instances')
        lines.append('\t\t\t(project "sony-5.1-revival"')
        lines.append(f'\t\t\t\t(path "/{ROOT_UUID}"')
        lines.append(f'\t\t\t\t\t(page "{pg}")')
        lines.append('\t\t\t\t)')
        lines.append('\t\t\t)')
        lines.append('\t\t)')
        lines.append('\t)')
        
    lines.append('\t(sheet_instances')
    lines.append('\t\t(path "/"')
    lines.append('\t\t\t(page "1")')
    lines.append('\t\t)')
    for name, filename, suuid, x, y, pg in sheets_info:
        lines.append(f'\t\t(path "/{suuid}"')
        lines.append(f'\t\t\t(page "{pg}")')
        lines.append('\t\t)')
    lines.append('\t)')
    
    lines.append(')')
    with open(f"{BASE}/sony-5.1-revival.kicad_sch", "w") as f:
        f.write('\n'.join(lines))
    print("Master root schematic built.")

# -------------------------------------------------------------
# 4. BUILD POWER SUPPLY SHEET
# -------------------------------------------------------------
def build_power_supply_sheet(lib_syms):
    s_uuid = SHEET_UUIDS["power_supply"]
    s_path = f"/{ROOT_UUID}/{s_uuid}"
    lines = []
    lines.append('(kicad_sch')
    lines.append('\t(version 20250114)')
    lines.append('\t(generator "eeschema")')
    lines.append('\t(generator_version "10.0")')
    lines.append(f'\t(uuid "{s_uuid}")')
    lines.append('\t(paper "A3")')
    lines.append('\t(title_block (title "Power Supply Subsystem (24V / 5V / 3.3V / 12V VGND)") (date "2026-09-06") (rev "1.0"))')
    lines.append('\t(lib_symbols')
    lines.append(lib_syms)
    lines.append('\t)')
    
    # 230V AC Mains & Inrush Protection
    lines.append(generate_placed_symbol("Connector:Conn_01x03", "J_AC", "230V_MAINS_L_N_E", 50.8, 76.2, 0, s_path, 3, "TerminalBlock:TerminalBlock_1x03_P5.08mm"))
    lines.append(generate_placed_symbol("Device:R", "F1", "FUSE_3A_250V", 76.2, 76.2, 90, s_path, 2, "Fuse:Fuseholder_5x20mm_Schurter_0031_8201"))
    lines.append(generate_placed_symbol("Device:R", "RV1", "14D431K_MOV", 93.98, 88.9, 0, s_path, 2, "Varistor:RV_Disc_D14mm_W3.8mm_P7.5mm"))
    
    # Bridge Rectifier & 9400uF Bulk Reservoir
    lines.append(generate_placed_symbol("sony-revival:KBU810", "BR1", "KBU810_8A_1000V", 119.38, 76.2, 0, s_path, 4, "Diode_THT:Diode_Bridge_Vishay_KBU"))
    lines.append(generate_placed_symbol("Device:C_Polarized", "C1", "4700uF_35V", 144.78, 76.2, 0, s_path, 2, "Capacitor_THT:CP_Radial_D18.0mm_P7.50mm"))
    lines.append(generate_placed_symbol("Device:C_Polarized", "C2", "4700uF_35V", 160.02, 76.2, 0, s_path, 2, "Capacitor_THT:CP_Radial_D18.0mm_P7.50mm"))
    lines.append(generate_placed_symbol("Device:C", "C3", "100nF_50V", 175.26, 76.2, 0, s_path, 2, "Capacitor_SMD:C_0805_2012Metric"))
    lines.append(generate_placed_symbol("Device:C", "C4", "100nF_50V", 187.96, 76.2, 0, s_path, 2, "Capacitor_SMD:C_0805_2012Metric"))
    
    # 5V Step-Down Buck Converter (LM2596-5.0)
    lines.append(generate_placed_symbol("sony-revival:LM2596_5V", "U_BUCK", "LM2596_5V_3A", 215.9, 76.2, 0, s_path, 5, "Package_TO_SOT_SMD:TO-263-5_TabPin3"))
    lines.append(generate_placed_symbol("Device:D", "D_BUCK", "1N5822_Schottky", 233.68, 88.9, 90, s_path, 2, "Diode_SMD:D_SMC"))
    lines.append(generate_placed_symbol("Device:L", "L_BUCK", "33uH_3A", 246.38, 76.2, 90, s_path, 2, "Inductor_SMD:L_12x12mm_H6mm"))
    lines.append(generate_placed_symbol("Device:C_Polarized", "C_BUCK_OUT", "220uF_16V", 261.62, 76.2, 0, s_path, 2, "Capacitor_SMD:CP_Elec_8x10.5"))
    
    # 3.3V Linear LDO (AMS1117-3.3)
    lines.append(generate_placed_symbol("sony-revival:AMS1117_3V3", "U_LDO", "AMS1117_3.3V", 292.1, 76.2, 0, s_path, 3, "Package_TO_SOT_SMD:SOT-223-3_TabPin2"))
    lines.append(generate_placed_symbol("Device:C", "C_LDO_IN", "10uF", 279.4, 76.2, 0, s_path, 2, "Capacitor_SMD:C_0805_2012Metric"))
    lines.append(generate_placed_symbol("Device:C", "C_LDO_OUT", "22uF", 309.88, 76.2, 0, s_path, 2, "Capacitor_SMD:C_0805_2012Metric"))
    
    # Precision Virtual Ground Rail Splitter (TLE2426)
    lines.append(generate_placed_symbol("sony-revival:TLE2426", "U_VGND", "TLE2426_12V", 144.78, 127.0, 0, s_path, 3, "Package_TO_SOT_THT:TO-92_Inline"))
    lines.append(generate_placed_symbol("Device:C_Polarized", "C_VGND", "100uF_25V", 162.56, 127.0, 0, s_path, 2, "Capacitor_THT:CP_Radial_D8.0mm_P3.50mm"))
    
    # Power Indicator LED
    lines.append(generate_placed_symbol("Device:D", "D_PWR", "GREEN_LED", 325.12, 76.2, 0, s_path, 2, "LED_SMD:LED_0805_2012Metric"))
    lines.append(generate_placed_symbol("Device:R", "R_PWR", "1k_1%", 337.82, 76.2, 0, s_path, 2, "Resistor_SMD:R_0805_2012Metric"))
    
    # Global Labels
    psu_labels = [
        ("AC_LIVE", 50.8, 60.96),
        ("AC_NEUTRAL", 50.8, 68.58),
        ("VCC_24V_RAW", 195.58, 60.96),
        ("VCC_24V", 195.58, 71.12),
        ("VCC_5V", 269.24, 60.96),
        ("VCC_3V3", 317.5, 60.96),
        ("VGND_12V", 172.72, 127.0),
        ("GND", 101.6, 114.3)
    ]
    for lbl, lx, ly in psu_labels:
        lines.append(f'\t(global_label "{lbl}" (shape bidirectional) (at {lx:.2f} {ly:.2f} 0) (fields_autoplaced yes) (effects (font (size 1.27 1.27)) (justify left)) (uuid "{make_uid()}"))')
        lines.append(f'\t(wire (pts (xy {lx-5.08:.2f} {ly:.2f}) (xy {lx:.2f} {ly:.2f})) (stroke (width 0) (type default)) (uuid "{make_uid()}"))')

    lines.append(')')
    with open(f"{BASE}/power_supply.kicad_sch", "w") as f:
        f.write('\n'.join(lines))
    print("Power supply sheet built.")

# -------------------------------------------------------------
# 5. BUILD AMPLIFIER SHEET (6 Channels, 3x TPA3116D2)
# -------------------------------------------------------------
def build_amplifier_sheet(lib_syms):
    s_uuid = SHEET_UUIDS["amplifier"]
    s_path = f"/{ROOT_UUID}/{s_uuid}"
    lines = []
    lines.append('(kicad_sch')
    lines.append('\t(version 20250114)')
    lines.append('\t(generator "eeschema")')
    lines.append('\t(generator_version "10.0")')
    lines.append(f'\t(uuid "{s_uuid}")')
    lines.append('\t(paper "A3")')
    lines.append('\t(title_block (title "6-Channel Class-D Amplifier Subsystem (3x TPA3116D2)") (date "2026-09-06") (rev "1.0"))')
    lines.append('\t(lib_symbols')
    lines.append(lib_syms)
    lines.append('\t)')
    
    # IC1: Front Left / Front Right (Gain: 26dB)
    lines.append(generate_placed_symbol("sony-revival:TPA3116D2", "U_AMP1", "TPA3116D2_FL_FR", 101.6, 88.9, 0, s_path, 21, "Package_SO:HTSSOP-32-1EP_6.1x11mm_P0.65mm_EP5.2x11mm"))
    # IC2: Surround Left / Surround Right (Gain: 20dB)
    lines.append(generate_placed_symbol("sony-revival:TPA3116D2", "U_AMP2", "TPA3116D2_SL_SR", 203.2, 88.9, 0, s_path, 21, "Package_SO:HTSSOP-32-1EP_6.1x11mm_P0.65mm_EP5.2x11mm"))
    # IC3: Center / Subwoofer (Gain: 26dB)
    lines.append(generate_placed_symbol("sony-revival:TPA3116D2", "U_AMP3", "TPA3116D2_C_SUB", 304.8, 88.9, 0, s_path, 21, "Package_SO:HTSSOP-32-1EP_6.1x11mm_P0.65mm_EP5.2x11mm"))
    
    # Output Reconstruction LC Filters (12 Inductors + 12 Capacitors)
    for i in range(1, 13):
        col = (i - 1) % 4
        row = (i - 1) // 4
        bx = 88.9 + (row * 101.6) + (col * 17.78)
        lines.append(generate_placed_symbol("Device:L", f"L{i}", "22uH_5A", bx, 139.7, 0, s_path, 2, "Inductor_SMD:L_12x12mm_H6mm"))
        lines.append(generate_placed_symbol("Device:C", f"C_O{i}", "680nF_63V", bx, 157.48, 0, s_path, 2, "Capacitor_THT:C_Rect_L7.2mm_W4.5mm_P5.00mm"))

    # Fail-safe mute pull-down (hardware mute on reset/dead ESP32)
    lines.append(generate_placed_symbol("Device:R", "R_MUTE_PD", "10k_FAILSAFE", 60.96, 152.4, 0, s_path, 2, "Resistor_SMD:R_0805_2012Metric"))

    amp_labels = [
        ("VCC_24V", 50.8, 50.8),
        ("GND", 50.8, 60.96),
        ("MUTE_ALL", 50.8, 71.12),
        ("FAULT1", 50.8, 81.28),
        ("FAULT2", 50.8, 91.44),
        ("FAULT3", 50.8, 101.6),
        ("HPF_FL", 50.8, 114.3),
        ("HPF_FR", 50.8, 124.46),
        ("HPF_SL", 165.1, 114.3),
        ("HPF_SR", 165.1, 124.46),
        ("CENTER_OUT", 266.7, 114.3),
        ("SUB_OUT", 266.7, 124.46),
        ("SPK_FL_P", 114.3, 177.8),
        ("SPK_FL_N", 127.0, 177.8),
        ("SPK_FR_P", 139.7, 177.8),
        ("SPK_FR_N", 152.4, 177.8),
        ("SPK_SL_P", 215.9, 177.8),
        ("SPK_SL_N", 228.6, 177.8),
        ("SPK_SR_P", 241.3, 177.8),
        ("SPK_SR_N", 254.0, 177.8),
        ("SPK_C_P", 317.5, 177.8),
        ("SPK_C_N", 330.2, 177.8),
        ("SPK_SUB_P", 342.9, 177.8),
        ("SPK_SUB_N", 355.6, 177.8)
    ]
    for lbl, lx, ly in amp_labels:
        lines.append(f'\t(global_label "{lbl}" (shape bidirectional) (at {lx:.2f} {ly:.2f} 0) (fields_autoplaced yes) (effects (font (size 1.27 1.27)) (justify left)) (uuid "{make_uid()}"))')
        lines.append(f'\t(wire (pts (xy {lx-5.08:.2f} {ly:.2f}) (xy {lx:.2f} {ly:.2f})) (stroke (width 0) (type default)) (uuid "{make_uid()}"))')

    lines.append(')')
    with open(f"{BASE}/amplifier.kicad_sch", "w") as f:
        f.write('\n'.join(lines))
    print("Amplifier sheet built.")

# -------------------------------------------------------------
# 6. BUILD CROSSOVER & INPUT SHEET (BT/AUX/USB, MUX, VOL, 3x NE5532)
# -------------------------------------------------------------
def build_crossover_sheet(lib_syms):
    s_uuid = SHEET_UUIDS["crossover_input"]
    s_path = f"/{ROOT_UUID}/{s_uuid}"
    lines = []
    lines.append('(kicad_sch')
    lines.append('\t(version 20250114)')
    lines.append('\t(generator "eeschema")')
    lines.append('\t(generator_version "10.0")')
    lines.append(f'\t(uuid "{s_uuid}")')
    lines.append('\t(paper "A3")')
    lines.append('\t(title_block (title "Active Crossover & Audio Input Stage") (date "2026-09-06") (rev "1.0"))')
    lines.append('\t(lib_symbols')
    lines.append(lib_syms)
    lines.append('\t)')
    
    # Input Connectors & Bluetooth
    lines.append(generate_placed_symbol("Connector:Conn_01x03", "J_AUX", "3.5mm_STEREO_AUX", 50.8, 76.2, 0, s_path, 3, "Connector_Audio:Jack_3.5mm_CUI_SJ1-3523N_Horizontal"))
    lines.append(generate_placed_symbol("Connector:Conn_01x03", "J_USB_IN", "USB_AUDIO_L_R", 50.8, 101.6, 0, s_path, 3, "Connector_PinHeader_2.54mm:PinHeader_1x03_P2.54mm_Vertical"))
    lines.append(generate_placed_symbol("sony-revival:QCC3008_MODULE", "U_BT", "QCC3008_BT5_APTX", 50.8, 139.7, 0, s_path, 12, "Connector_PinHeader_2.54mm:PinHeader_1x12_P2.54mm_Vertical"))
    
    # Dual 4:1 Analog Mux & SPI Digital Potentiometer
    lines.append(generate_placed_symbol("sony-revival:CD4052", "U_MUX", "CD4052_AUDIO_MUX", 93.98, 88.9, 0, s_path, 16, "Package_SO:SOIC-16_3.9x9.9mm_P1.27mm"))
    lines.append(generate_placed_symbol("sony-revival:MCP4252", "U_VOL", "MCP4252_SPI_POT", 137.16, 88.9, 0, s_path, 14, "Package_SO:SOIC-14_3.9x8.7mm_P1.27mm"))
    
    # Active Crossover: 3x NE5532 Dual Op-Amps
    lines.append(generate_placed_symbol("sony-revival:NE5532", "U_OP1", "NE5532_HPF_80HZ_LR", 182.88, 88.9, 0, s_path, 8, "Package_SO:SOIC-8_3.9x4.9mm_P1.27mm"))
    lines.append(generate_placed_symbol("sony-revival:NE5532", "U_OP2", "NE5532_MONO_SUM", 228.6, 88.9, 0, s_path, 8, "Package_SO:SOIC-8_3.9x4.9mm_P1.27mm"))
    lines.append(generate_placed_symbol("sony-revival:NE5532", "U_OP3", "NE5532_LPF_80HZ_SUB", 274.32, 88.9, 0, s_path, 8, "Package_SO:SOIC-8_3.9x4.9mm_P1.27mm"))
    
    # Crossover Precision Passives
    for c in range(1, 7):
        cx = 160.0 + (c * 20.32)
        lines.append(generate_placed_symbol("Device:R", f"R_F{c}", "20k_1%", cx, 127.0, 0, s_path, 2, "Resistor_SMD:R_0805_2012Metric"))
        lines.append(generate_placed_symbol("Device:C", f"C_F{c}", "100nF_FILM", cx, 147.32, 0, s_path, 2, "Capacitor_THT:C_Rect_L7.2mm_W4.5mm_P5.00mm"))

    cross_labels = [
        ("VCC_24V", 50.8, 50.8),
        ("VGND_12V", 50.8, 58.42),
        ("GND", 50.8, 66.04),
        ("MUX_A", 93.98, 50.8),
        ("MUX_B", 93.98, 58.42),
        ("VOL_CS", 137.16, 50.8),
        ("SPI_SCK", 137.16, 58.42),
        ("SPI_MOSI", 137.16, 66.04),
        ("SPI_MISO", 137.16, 73.66),
        ("BT_KEY", 50.8, 165.1),
        ("HPF_FL", 325.12, 76.2),
        ("HPF_FR", 325.12, 88.9),
        ("HPF_SL", 325.12, 101.6),
        ("HPF_SR", 325.12, 114.3),
        ("CENTER_OUT", 325.12, 127.0),
        ("SUB_OUT", 325.12, 139.7)
    ]
    for lbl, lx, ly in cross_labels:
        lines.append(f'\t(global_label "{lbl}" (shape bidirectional) (at {lx:.2f} {ly:.2f} 0) (fields_autoplaced yes) (effects (font (size 1.27 1.27)) (justify left)) (uuid "{make_uid()}"))')
        lines.append(f'\t(wire (pts (xy {lx-5.08:.2f} {ly:.2f}) (xy {lx:.2f} {ly:.2f})) (stroke (width 0) (type default)) (uuid "{make_uid()}"))')

    lines.append(')')
    with open(f"{BASE}/crossover_input.kicad_sch", "w") as f:
        f.write('\n'.join(lines))
    print("Crossover sheet built.")

# -------------------------------------------------------------
# 7. BUILD CONTROLLER SHEET (ESP32, OLED, Encoder, IR, CLI UART)
# -------------------------------------------------------------
def build_controller_sheet(lib_syms):
    s_uuid = SHEET_UUIDS["controller"]
    s_path = f"/{ROOT_UUID}/{s_uuid}"
    lines = []
    lines.append('(kicad_sch')
    lines.append('\t(version 20250114)')
    lines.append('\t(generator "eeschema")')
    lines.append('\t(generator_version "10.0")')
    lines.append(f'\t(uuid "{s_uuid}")')
    lines.append('\t(paper "A3")')
    lines.append('\t(title_block (title "ESP32 Controller & Telemetry Subsystem") (date "2026-09-06") (rev "1.0"))')
    lines.append('\t(lib_symbols')
    lines.append(lib_syms)
    lines.append('\t)')
    
    # ESP32 Main Processor
    lines.append(generate_placed_symbol("sony-revival:ESP32_WROOM_32", "U_MCU", "ESP32-WROOM-32", 152.4, 101.6, 0, s_path, 30, "RF_Module:ESP32-WROOM-32"))
    
    # 2.42" OLED SPI Plug & Play Header (7-pin)
    lines.append(generate_placed_symbol("Connector:Conn_01x07", "J_OLED", "OLED_SPI_2.42in", 63.5, 76.2, 0, s_path, 7, "Connector_PinHeader_2.54mm:PinHeader_1x07_P2.54mm_Vertical"))
    # Rotary Encoder Header (5-pin)
    lines.append(generate_placed_symbol("Connector:Conn_01x05", "J_ENC", "ROTARY_ENCODER_SW", 63.5, 114.3, 0, s_path, 5, "Connector_PinHeader_2.54mm:PinHeader_1x05_P2.54mm_Vertical"))
    # USB Serial Control Port / Programming Header (4-pin)
    lines.append(generate_placed_symbol("Connector:Conn_01x04", "J_CTRL", "UART_CLI_CTRL_PORT", 63.5, 147.32, 0, s_path, 4, "Connector_PinHeader_2.54mm:PinHeader_1x04_P2.54mm_Vertical"))
    # IR Remote Receiver
    lines.append(generate_placed_symbol("sony-revival:TSOP1738", "U_IR", "TSOP1738_IR_38KHZ", 63.5, 177.8, 0, s_path, 3, "OptoDevice:Vishay_MINIMOLD-3Pin"))
    
    # Status LED & Resistor
    lines.append(generate_placed_symbol("Device:D", "D_STATUS", "BLUE_LED", 241.3, 76.2, 0, s_path, 2, "LED_SMD:LED_0805_2012Metric"))
    lines.append(generate_placed_symbol("Device:R", "R_STATUS", "1k_1%", 256.54, 76.2, 0, s_path, 2, "Resistor_SMD:R_0805_2012Metric"))
    
    # Telemetry ADC Conditioning (NTC & DC Offset)
    lines.append(generate_placed_symbol("Device:C", "C_ADC1", "100nF_ADC_FILT", 241.3, 101.6, 0, s_path, 2, "Capacitor_SMD:C_0805_2012Metric"))
    lines.append(generate_placed_symbol("Device:C", "C_ADC2", "100nF_ADC_FILT", 256.54, 101.6, 0, s_path, 2, "Capacitor_SMD:C_0805_2012Metric"))

    ctrl_labels = [
        ("VCC_5V", 50.8, 50.8),
        ("VCC_3V3", 50.8, 58.42),
        ("GND", 50.8, 66.04),
        ("MUTE_ALL", 127.0, 50.8),
        ("RELAY_CTRL", 127.0, 58.42),
        ("STATUS_LED", 127.0, 66.04),
        ("SPI_SCK", 203.2, 50.8),
        ("SPI_MOSI", 203.2, 58.42),
        ("SPI_MISO", 203.2, 66.04),
        ("VOL_CS", 203.2, 73.66),
        ("MUX_A", 203.2, 81.28),
        ("MUX_B", 203.2, 88.9),
        ("BT_KEY", 203.2, 96.52),
        ("FAULT1", 284.48, 50.8),
        ("FAULT2", 284.48, 58.42),
        ("FAULT3", 284.48, 66.04),
        ("NTC_ADC", 284.48, 76.2),
        ("DC_OFFSET_ADC", 284.48, 86.36)
    ]
    for lbl, lx, ly in ctrl_labels:
        lines.append(f'\t(global_label "{lbl}" (shape bidirectional) (at {lx:.2f} {ly:.2f} 0) (fields_autoplaced yes) (effects (font (size 1.27 1.27)) (justify left)) (uuid "{make_uid()}"))')
        lines.append(f'\t(wire (pts (xy {lx-5.08:.2f} {ly:.2f}) (xy {lx:.2f} {ly:.2f})) (stroke (width 0) (type default)) (uuid "{make_uid()}"))')

    lines.append(')')
    with open(f"{BASE}/controller.kicad_sch", "w") as f:
        f.write('\n'.join(lines))
    print("Controller sheet built.")

# -------------------------------------------------------------
# 8. BUILD PROTECTION & TERMINALS SHEET
# -------------------------------------------------------------
def build_protection_sheet(lib_syms):
    s_uuid = SHEET_UUIDS["protection"]
    s_path = f"/{ROOT_UUID}/{s_uuid}"
    lines = []
    lines.append('(kicad_sch')
    lines.append('\t(version 20250114)')
    lines.append('\t(generator "eeschema")')
    lines.append('\t(generator_version "10.0")')
    lines.append(f'\t(uuid "{s_uuid}")')
    lines.append('\t(paper "A3")')
    lines.append('\t(title_block (title "Protection & Output Speaker Terminals") (date "2026-09-06") (rev "1.0"))')
    lines.append('\t(lib_symbols')
    lines.append(lib_syms)
    lines.append('\t)')
    
    # 24V Main Power Relay (10A) & Driver
    lines.append(generate_placed_symbol("sony-revival:RELAY_SPST", "K1", "RELAY_10A_24V_DISC", 88.9, 76.2, 0, s_path, 4, "Relay_THT:Relay_SPST_SANYOU_SRD_Series_Form_A"))
    lines.append(generate_placed_symbol("sony-revival:2N2222", "Q1", "2N2222_RELAY_DRV", 88.9, 101.6, 0, s_path, 3, "Package_TO_SOT_THT:TO-92_Inline"))
    lines.append(generate_placed_symbol("Device:D", "D_FLY", "1N4007_FLYBACK", 106.68, 76.2, 90, s_path, 2, "Diode_SMD:D_SMA"))
    lines.append(generate_placed_symbol("Device:R", "R_BASE", "1k_1%", 71.12, 101.6, 0, s_path, 2, "Resistor_SMD:R_0805_2012Metric"))

    # DC Offset Sense Network
    lines.append(generate_placed_symbol("Device:R", "R_DC1", "100k_1%", 144.78, 76.2, 0, s_path, 2, "Resistor_SMD:R_0805_2012Metric"))
    lines.append(generate_placed_symbol("Device:R", "R_DC2", "10k_1%", 162.56, 76.2, 0, s_path, 2, "Resistor_SMD:R_0805_2012Metric"))
    lines.append(generate_placed_symbol("Device:C", "C_DC_FILT", "10uF_25V", 180.34, 76.2, 0, s_path, 2, "Capacitor_SMD:C_0805_2012Metric"))

    # Heatsink NTC Voltage Divider
    lines.append(generate_placed_symbol("Device:R", "R_NTC_PU", "10k_0.1%", 215.9, 76.2, 0, s_path, 2, "Resistor_SMD:R_0805_2012Metric"))
    lines.append(generate_placed_symbol("Device:R", "TH1", "10k_NTC_HEATSINK", 233.68, 76.2, 0, s_path, 2, "Resistor_SMD:R_0805_2012Metric"))

    # 6 Channel Speaker Output Polyfuses (2A PTC) and Heavy-Duty Screw Terminals
    spk_names = ["FL", "FR", "SL", "SR", "CENTER", "SUB"]
    for i, name in enumerate(spk_names, 1):
        sx = 88.9 + ((i - 1) * 45.72)
        lines.append(generate_placed_symbol("Device:R", f"PF{i}", "2A_PTC_POLYFUSE", sx, 127.0, 90, s_path, 2, "Fuse:Fuse_1812_4532Metric"))
        lines.append(generate_placed_symbol("Connector:Conn_01x02", f"J_SPK_{name}", f"SPK_{name}_TERM", sx, 152.4, 0, s_path, 2, "TerminalBlock:TerminalBlock_1x02_P5.08mm"))

    prot_labels = [
        ("VCC_24V_RAW", 50.8, 50.8),
        ("VCC_24V", 50.8, 58.42),
        ("VCC_5V", 50.8, 66.04),
        ("RELAY_CTRL", 50.8, 73.66),
        ("GND", 50.8, 81.28),
        ("NTC_ADC", 248.92, 76.2),
        ("DC_OFFSET_ADC", 195.58, 76.2),
        ("SPK_FL_P", 76.2, 114.3),
        ("SPK_FL_N", 88.9, 114.3),
        ("SPK_FR_P", 121.92, 114.3),
        ("SPK_FR_N", 134.62, 114.3),
        ("SPK_SL_P", 167.64, 114.3),
        ("SPK_SL_N", 180.34, 114.3),
        ("SPK_SR_P", 213.36, 114.3),
        ("SPK_SR_N", 226.06, 114.3),
        ("SPK_C_P", 259.08, 114.3),
        ("SPK_C_N", 271.78, 114.3),
        ("SPK_SUB_P", 304.8, 114.3),
        ("SPK_SUB_N", 317.5, 114.3)
    ]
    for lbl, lx, ly in prot_labels:
        lines.append(f'\t(global_label "{lbl}" (shape bidirectional) (at {lx:.2f} {ly:.2f} 0) (fields_autoplaced yes) (effects (font (size 1.27 1.27)) (justify left)) (uuid "{make_uid()}"))')
        lines.append(f'\t(wire (pts (xy {lx-5.08:.2f} {ly:.2f}) (xy {lx:.2f} {ly:.2f})) (stroke (width 0) (type default)) (uuid "{make_uid()}"))')

    lines.append(')')
    with open(f"{BASE}/protection.kicad_sch", "w") as f:
        f.write('\n'.join(lines))
    print("Protection sheet built.")

# -------------------------------------------------------------
# MAIN EXECUTION
# -------------------------------------------------------------
if __name__ == "__main__":
    for lck in ["~amplifier.kicad_sch.lck", "~sony-5.1-revival.kicad_sch.lck"]:
        p = f"{BASE}/{lck}"
        if os.path.exists(p):
            try:
                os.remove(p)
                print(f"Removed lock file: {lck}")
            except Exception:
                pass

    print("Building custom symbol library...")
    build_custom_symbol_library()
    
    lib_syms = get_common_lib_symbols()
    
    print("Building all schematic sheets...")
    build_root_schematic()
    build_power_supply_sheet(lib_syms)
    build_amplifier_sheet(lib_syms)
    build_crossover_sheet(lib_syms)
    build_controller_sheet(lib_syms)
    build_protection_sheet(lib_syms)
    
    print("\n--- ALL KICAD SCHEMATIC FILES BUILT SUCCESSFULLY ---")
